49bitcat/nileswan/legacy/pcb/snapeda/models/SIT8021AI-J4-XXS-24.000000E.step

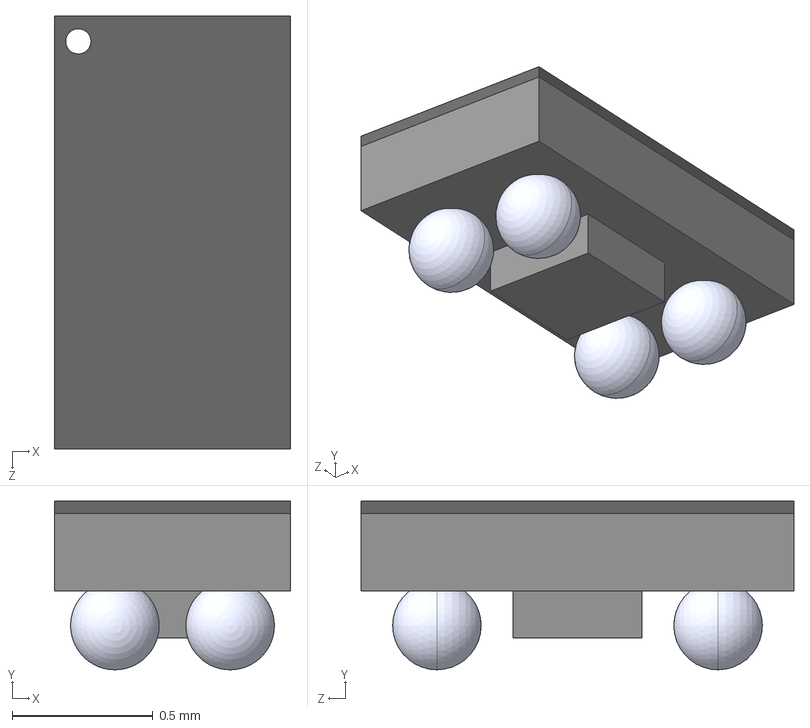
[picture p17: CAD file, 2025-10-31, an earlier design]
legacy/pcb/snapeda/models/SIT8021AI-J4-XXS-24.000000E.step
0.84 x 0.6 x 1.54 mm
