49bitcat/nileswan/legacy/pcb/snapeda/models/W25Q16JVZPIQ.STEP

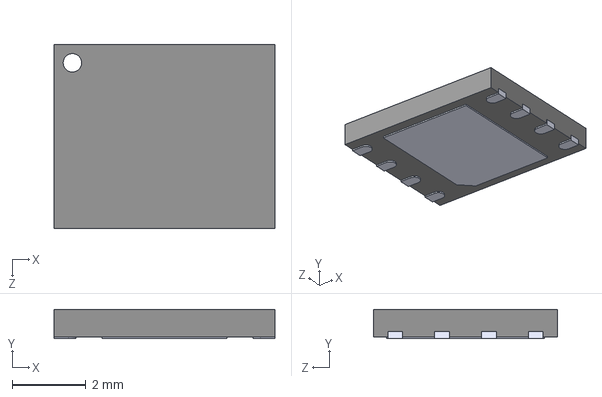
[picture p18: CAD file, 2025-10-31, an earlier design]
legacy/pcb/snapeda/models/W25Q16JVZPIQ.STEP
6.00 x 0.8 x 5.00 mm
