49bitcat/nileswan/legacy/pcb/snapeda/models/TPS3619-50DGK.step

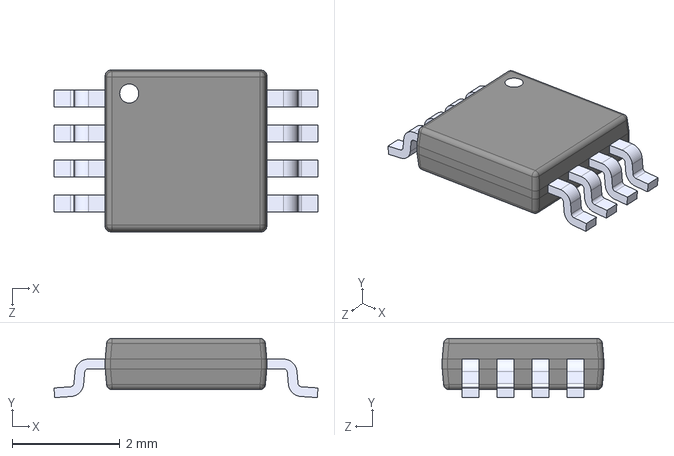
[picture p19: CAD file, 2025-10-31, an earlier design]
legacy/pcb/snapeda/models/TPS3619-50DGK.step
4.90 x 1.10 x 3.00 mm
