49bitcat/nileswan/firmware/src/mcu.c

/**
 * Copyright (c) 2024 Adrian "asie" Siekierka
 *
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
 * You should have received a copy of the GNU General Public License along
 * with Nileswan MCU. If not, see <https://www.gnu.org/licenses/>.
 */

#include <stdbool.h>
#include <stddef.h>
#include <stdint.h>
#include <stm32u073xx.h>
#include <stm32u0xx_ll_adc.h>
#include <stm32u0xx_ll_gpio.h>
#include <stm32u0xx_ll_pwr.h>
#include <stm32u0xx_ll_rcc.h>
#include <stm32u0xx_ll_system.h>

#include "mcu.h"
#include "config.h"
#include "nvram.h"
#include "rtc.h"
#include "spi.h"
#include "tusb.h"
#include "accel.h"

typedef enum {
    USB_INIT_STATUS_OFF = 0,
    USB_INIT_STATUS_REQUEST_ON = 1,
    USB_INIT_STATUS_ON = 2,
    USB_INIT_STATUS_REQUEST_OFF = 3
} usb_init_status_t;

static bool usb_enabled = false;
static volatile uint8_t usb_init_status = USB_INIT_STATUS_OFF;

static void __mcu_usb_on_power_change(void) {
    if (mcu_usb_is_power_connected() && usb_enabled) {
        if (usb_init_status == USB_INIT_STATUS_OFF) {
            usb_init_status = USB_INIT_STATUS_REQUEST_ON;
        } else if (usb_init_status == USB_INIT_STATUS_ON) {
            USB->BCDR |= USB_BCDR_DPPU;
        }
    } else {
        if (usb_init_status == USB_INIT_STATUS_ON) {
            usb_init_status = USB_INIT_STATUS_REQUEST_OFF;
        }
    }
}

#define BATTERY_QUERY_DELAY (48 / 3)

enum {
    BATTERY_PRESENT_CACHE_UNKNOWN = 0,
    BATTERY_PRESENT_CACHE_NO,
    BATTERY_PRESENT_CACHE_YES
};

static uint8_t battery_present_cache = BATTERY_PRESENT_CACHE_UNKNOWN;

uint16_t mcu_power_query_battery_voltage(void) {
    int i;

    // Before running an ADC measurement, we need to rule out the case of the
    // battery being removed (floating BAT pin). However, as using a pull-down
    // here is electrically costly, we want to avoid doing it more often than
    // necessary. With this in mind, the following assumptions are made:
    //
    // - If the MCU is running in a console, the cartridge is designed so that
    //   the battery should not be removed. As such, we can make an assumption
    //   that it is either present or not present after the first check.
    // - If the MCU is running outside of a console, we can assume that the
    //   battery is inserted; otherwise, the code would not be running.
    if (!mcu_power_is_running_on_battery()) {
        if (battery_present_cache == BATTERY_PRESENT_CACHE_UNKNOWN) {
            // Figure out if the battery is present.
            LL_GPIO_SetPinMode(GPIOB, MCU_PIN_BAT, LL_GPIO_MODE_INPUT);
            LL_GPIO_SetPinPull(GPIOB, MCU_PIN_BAT, LL_GPIO_PULL_DOWN);
            i = BATTERY_QUERY_DELAY; while (i--) asm("");
            bool battery_present = LL_GPIO_IsInputPinSet(GPIOB, MCU_PIN_BAT);
            LL_GPIO_SetPinMode(GPIOB, MCU_PIN_BAT, LL_GPIO_MODE_ANALOG);
            LL_GPIO_SetPinPull(GPIOB, MCU_PIN_BAT, LL_GPIO_PULL_NO);
            battery_present_cache = battery_present ? BATTERY_PRESENT_CACHE_YES : BATTERY_PRESENT_CACHE_NO;
        }

        if (battery_present_cache == BATTERY_PRESENT_CACHE_NO) {
            return 0;
        }
    } else {
        battery_present_cache = BATTERY_PRESENT_CACHE_YES;
    }

    i = BATTERY_QUERY_DELAY; while (i--) asm("");

    // Once we have figured out that the battery is present,
    // measure the exact voltage if enabled.
#ifdef CONFIG_ENABLE_ADC
    if (LL_ADC_IsEnabled(ADC1)) {
        LL_ADC_REG_StartConversion(ADC1);
        while (!LL_ADC_IsActiveFlag_EOC(ADC1));
        return LL_ADC_REG_ReadConversionData12(ADC1);
    }
#endif
    return 3725; // ~3.0V
}

static void __mcu_bat_on_power_change(void) {
    // If battery inserted and running on battery, go to Standby
    if (mcu_power_is_running_on_battery() && mcu_power_is_battery_inserted()) {
        mcu_shutdown();
    }
}

void PVD_PVM_IRQHandler(void) {
    mcu_shutdown();
}

void EXTI2_3_IRQHandler(void) {
    if ((EXTI->RPR1 & EXTI_RPR1_RPIF2) != 0) {
        EXTI->RPR1 = EXTI_RPR1_RPIF2;
        mcu_spi_irq_set(MCU_SPI_IRQ_TF_REMOVE);
    }

    if ((EXTI->FPR1 & EXTI_FPR1_FPIF2) != 0) {
        EXTI->FPR1 = EXTI_FPR1_FPIF2;
        mcu_spi_irq_set(MCU_SPI_IRQ_TF_INSERT);
    }
}

void EXTI4_15_IRQHandler(void) {
    if ((EXTI->RPR1 & EXTI_RPR1_RPIF5) != 0) {
        EXTI->RPR1 = EXTI_RPR1_RPIF5;
        __mcu_usb_on_power_change();
    }

    if ((EXTI->FPR1 & EXTI_FPR1_FPIF5) != 0) {
        EXTI->FPR1 = EXTI_FPR1_FPIF5;
        __mcu_usb_on_power_change();
    }

    if ((EXTI->RPR1 & EXTI_RPR1_RPIF7) != 0) {
        EXTI->RPR1 = EXTI_RPR1_RPIF7;
        __mcu_bat_on_power_change();
    }

    if ((EXTI->FPR1 & EXTI_FPR1_FPIF7) != 0) {
        EXTI->FPR1 = EXTI_FPR1_FPIF7;
        __mcu_bat_on_power_change();
    }
}

static uint16_t last_clock_speed = 0xFFFF;
static uint8_t busy_pin_delay = 0;

#define FINISH_BUSY_MIN_CLOCKS 10
#define FINISH_BUSY_CLOCKS_PER_ITERATION 3

__attribute__((noinline))
void mcu_fpga_finish_busy(void) {
    // ~10 cycles + 3 cycles per iteration
    int i = busy_pin_delay;
    while (i--) asm("");
    LL_GPIO_SetPinMode(GPIOA, MCU_PIN_FPGA_BUSY, LL_GPIO_MODE_ANALOG);
}

void mcu_update_clock_speed(void) {
    uint32_t msi_range;
    uint32_t ahb_freq;
    uint32_t ahb_divisor;
    uint32_t apb_divisor;

    // Calculate target MCU speed
#ifdef CONFIG_MCU_FORCE_MAX_CLOCK
    msi_range = LL_RCC_MSIRANGE_11;
    ahb_freq = 48 * 1000 * 1000;
    ahb_divisor = LL_RCC_SYSCLK_DIV_1;
    apb_divisor = LL_RCC_APB1_DIV_1;
#else
    msi_range = LL_RCC_MSIRANGE_8;
    ahb_freq = 16 * 1000 * 1000;
    ahb_divisor = LL_RCC_SYSCLK_DIV_1;
    apb_divisor = LL_RCC_APB1_DIV_1;

    bool usb_power_connected = mcu_usb_is_power_connected() && usb_enabled;
    if (usb_power_connected
#ifndef CONFIG_ENABLE_CLOCK_MSI_USB
        && tud_mounted()
#endif
    ) {
        // If USB is plugged in, accelerate the CPU.
        switch (mcu_spi_get_freq()) {
            default:
                // 48 MHz AHB, 48 MHz APB
                msi_range = LL_RCC_MSIRANGE_11;
                ahb_freq = 48 * 1000 * 1000;
                break;
            case MCU_SPI_FREQ_384KHZ:
                // SPI bus constrained to 384 KHz - fast USB communication doesn't matter much.
                // 24 MHz AHB, 24 MHz APB
#ifdef CONFIG_ENABLE_CLOCK_MSI_USB
                msi_range = LL_RCC_MSIRANGE_11;
                ahb_divisor = LL_RCC_SYSCLK_DIV_2;
#else
                msi_range = LL_RCC_MSIRANGE_9;
#endif
                ahb_freq = 24 * 1000 * 1000;
                break;
        }
    } else {
        switch (mcu_spi_get_freq()) {
            case MCU_SPI_FREQ_384KHZ:
                if (usb_power_connected)
                    break;

                // For slow SPI transfers, we can clock the APB bus down.
                // 16 MHz AHB, 4 MHz APB
                apb_divisor = LL_RCC_APB1_DIV_4;

                if (mcu_spi_get_mode() == MCU_SPI_MODE_EEPROM || mcu_spi_get_mode() == MCU_SPI_MODE_CDC_OUTPUT) {
                    // 384 KHz SPI output only mode (EEPROM, USB CDC output w/o USB connected)
                    // 1 MHz AHB, 1 MHz APB
                    msi_range = LL_RCC_MSIRANGE_4;
                    ahb_freq = 1 * 1000 * 1000;
                    apb_divisor = LL_RCC_APB1_DIV_1;
                } else if (mcu_spi_get_mode() == MCU_SPI_MODE_RTC) {
                    // FIXME: The FPGA RTC logic appears to break down when the APB frequency is not divisible by 384 KHz.
                    // FIXME: At frequencies below 24 MHz, the RTC stability test still fails after a few hundred thousand attempts.
                    msi_range = LL_RCC_MSIRANGE_9;
                    ahb_freq = 24 * 1000 * 1000;
                    ahb_divisor = LL_RCC_SYSCLK_DIV_1;
                    apb_divisor = LL_RCC_APB1_DIV_1;
                } else {
                    // Other modes (f.e. native MCU mode)
                    // 8 MHz AHB, 4 MHz APB
                    msi_range = LL_RCC_MSIRANGE_7;
                    ahb_freq = 8 * 1000 * 1000;
                    apb_divisor = LL_RCC_APB1_DIV_2;
                }
                break;
            case MCU_SPI_FREQ_6MHZ:
                // 6 MHz SPI transfers.
                // 24 MHz AHB, 12/24 MHz APB
                msi_range = LL_RCC_MSIRANGE_9;
                ahb_freq = 24 * 1000 * 1000;
                if (!usb_power_connected)
                    apb_divisor = LL_RCC_APB1_DIV_2;
                break;
            case MCU_SPI_FREQ_24MHZ:
                // 24 MHz SPI transfers.
                // 48 MHz AHB, 48 MHz APB
                msi_range = LL_RCC_MSIRANGE_11;
                ahb_freq = 48 * 1000 * 1000;
                break;
        }
    }
#endif

    uint32_t apb_freq = ahb_freq;
    switch (apb_divisor) {
    case LL_RCC_APB1_DIV_1: break;
    case LL_RCC_APB1_DIV_2: apb_freq /= 2; break;
    case LL_RCC_APB1_DIV_4: apb_freq /= 4; break;
    case LL_RCC_APB1_DIV_8: apb_freq /= 8; break;
    case LL_RCC_APB1_DIV_16: apb_freq /= 16; break;
    }
    accel_adjust_i2c_timing(apb_freq);

    if ((msi_range | ahb_divisor) == last_clock_speed) {
        LL_RCC_SetAPB1Prescaler(apb_divisor);
        return;
    }

    bool use_high_flash_latency = msi_range > LL_RCC_MSIRANGE_9 && ahb_divisor == LL_RCC_SYSCLK_DIV_1;
    bool use_high_voltage_scale = msi_range >= LL_RCC_MSIRANGE_8;
    bool use_high_power_run = msi_range >= LL_RCC_MSIRANGE_5;

    LL_RCC_SetAPB1Prescaler(LL_RCC_APB1_DIV_1);

    if (use_high_power_run) {
        LL_PWR_DisableLowPowerRunMode();
        while (LL_PWR_IsEnabledLowPowerRunMode());
    }

    if (use_high_voltage_scale) {
        LL_PWR_SetRegulVoltageScaling(LL_PWR_REGU_VOLTAGE_SCALE1);
        while (LL_PWR_IsActiveFlag_VOS());
    }

    if (use_high_flash_latency) {
        LL_FLASH_SetLatency(LL_FLASH_LATENCY_1);
        while (LL_FLASH_GetLatency() != LL_FLASH_LATENCY_1);
    }

    LL_RCC_SetAHBPrescaler(LL_RCC_SYSCLK_DIV_1);

    while (!LL_RCC_MSI_IsReady());
    LL_RCC_MSI_SetRange(msi_range);

    if (!use_high_flash_latency)
        LL_FLASH_SetLatency(LL_FLASH_LATENCY_0);

    if (!use_high_voltage_scale) {
        LL_PWR_SetRegulVoltageScaling(LL_PWR_REGU_VOLTAGE_SCALE2);
        while (LL_PWR_IsActiveFlag_VOS());
    }

    if (!use_high_power_run) {
        LL_PWR_EnableLowPowerRunMode();
        while (!LL_PWR_IsEnabledLowPowerRunMode());
    }

    LL_RCC_SetAHBPrescaler(ahb_divisor);
    LL_RCC_SetAPB1Prescaler(apb_divisor);
    LL_SetSystemCoreClock(ahb_freq);
    LL_Init1msTick(ahb_freq);

#ifdef CONFIG_ENABLE_ADC
    uint32_t adc_clock = LL_ADC_CLOCK_SYNC_PCLK_DIV1;
    if (msi_range >= LL_RCC_MSIRANGE_10) {
        adc_clock = LL_ADC_CLOCK_SYNC_PCLK_DIV4;
    } else if (msi_range >= LL_RCC_MSIRANGE_8) {
        adc_clock = LL_ADC_CLOCK_SYNC_PCLK_DIV2;
    }
    LL_ADC_SetClock(ADC1, adc_clock);
#endif

    int clocks = (ahb_freq / (384*1000)) - FINISH_BUSY_MIN_CLOCKS;
    busy_pin_delay = clocks > 0 ? ((uint32_t)(clocks + FINISH_BUSY_CLOCKS_PER_ITERATION - 1) / FINISH_BUSY_CLOCKS_PER_ITERATION) : 0;

    last_clock_speed = (msi_range | ahb_divisor);
}

void mcu_init(void) {
    // Initialize clocks
    LL_RCC_MSI_Enable();

    LL_APB1_GRP1_EnableClock(LL_APB1_GRP1_PERIPH_PWR);
    LL_LPM_EnableSleep();

    while (!LL_RCC_MSI_IsReady());
    LL_RCC_MSI_EnableRangeSelection();

    mcu_update_clock_speed();

    LL_RCC_SetSysClkSource(LL_RCC_SYS_CLKSOURCE_MSI);
    while(LL_RCC_GetSysClkSource() != LL_RCC_SYS_CLKSOURCE_STATUS_MSI);

    LL_RCC_SetAHBPrescaler(LL_RCC_SYSCLK_DIV_1);

#ifdef TARGET_U0
    LL_APB1_GRP2_EnableClock(LL_APB1_GRP2_PERIPH_SYSCFG);
#else
    LL_RCC_SetAPB2Prescaler(LL_RCC_APB2_DIV_1);
    LL_APB2_GRP1_EnableClock(LL_APB2_GRP1_PERIPH_SYSCFG);
#endif

    LL_SYSTICK_SetClkSource(LL_SYSTICK_CLKSOURCE_HCLK);
    LL_SYSTICK_EnableIT();

    LL_PWR_EnableBkUpAccess();

    LL_IOP_GRP1_EnableClock(LL_IOP_GRP1_PERIPH_GPIOA | LL_IOP_GRP1_PERIPH_GPIOB);

    // Initialize input pins
    LL_GPIO_SetPinPull(GPIOA, MCU_PIN_TF_DETECT, LL_GPIO_PULL_UP);
    LL_GPIO_SetPinSpeed(GPIOA, MCU_PIN_TF_DETECT, LL_GPIO_SPEED_FREQ_LOW);
    LL_GPIO_SetPinMode(GPIOA, MCU_PIN_TF_DETECT, LL_GPIO_MODE_INPUT);

    // Initialize input pins: VBUS sensing
    LL_GPIO_SetPinPull(GPIOB, MCU_PIN_USB_POWER, LL_GPIO_PULL_DOWN);
    LL_GPIO_SetPinSpeed(GPIOB, MCU_PIN_USB_POWER, LL_GPIO_SPEED_FREQ_LOW);
    LL_GPIO_SetPinMode(GPIOB, MCU_PIN_USB_POWER, LL_GPIO_MODE_INPUT);

    // Initialize input pins: battery sensing
    LL_GPIO_SetPinPull(GPIOB, MCU_PIN_BAT, LL_GPIO_PULL_NO);
    LL_GPIO_SetPinSpeed(GPIOB, MCU_PIN_BAT, LL_GPIO_SPEED_FREQ_LOW);
    LL_GPIO_SetPinMode(GPIOB, MCU_PIN_BAT, LL_GPIO_MODE_ANALOG);
    LL_GPIO_SetPinPull(GPIOB, MCU_PIN_RUNS_ON_BAT, LL_GPIO_PULL_UP);
    LL_GPIO_SetPinSpeed(GPIOB, MCU_PIN_RUNS_ON_BAT, LL_GPIO_SPEED_FREQ_LOW);
    LL_GPIO_SetPinMode(GPIOB, MCU_PIN_RUNS_ON_BAT, LL_GPIO_MODE_INPUT);

    // Keep the pulls active in Standby mode
    PWR->PUCRA = 0;
    PWR->PUCRB = MCU_PIN_RUNS_ON_BAT;
    PWR->PDCRA = 0;
    PWR->PDCRB = MCU_PIN_USB_POWER;
    LL_PWR_EnablePUPDCfg();
    LL_PWR_EnableSRAMRetention();

    // Enable PVD - if we're below 2.9 V, we are definitely not plugged
    // into a console, so we can short circuit to powering down.
    LL_PWR_SetPVDLevel(LL_PWR_PVDLEVEL_6);
    LL_PWR_EnablePVD();

    LL_EXTI_EnableRisingTrig_0_31(LL_EXTI_LINE_16);
    LL_EXTI_EnableIT_0_31(LL_EXTI_LINE_16);
    NVIC_SetPriority(PVD_PVM_IRQn, MCU_IRQ_PRIORITY_PVD);
    NVIC_EnableIRQ(PVD_PVM_IRQn);

#ifdef CONFIG_ENABLE_ADC
    // Initialize ADC
    LL_APB1_GRP2_EnableClock(LL_APB1_GRP2_PERIPH_ADC);
    LL_ADC_SetResolution(ADC1, LL_ADC_RESOLUTION_12B);
    LL_ADC_SetDataAlignment(ADC1, LL_ADC_DATA_ALIGN_RIGHT);
    LL_ADC_REG_SetContinuousMode(ADC1, LL_ADC_REG_CONV_SINGLE);
    if (LL_ADC_REG_GetSequencerConfigurable(ADC1) != LL_ADC_REG_SEQ_FIXED) {
        LL_ADC_REG_SetSequencerConfigurable(ADC1, LL_ADC_REG_SEQ_FIXED);
        while (!LL_ADC_IsActiveFlag_CCRDY(ADC1));
        LL_ADC_ClearFlag_CCRDY(ADC1);
    }
    LL_ADC_SetSamplingTimeCommonChannels(ADC1, LL_ADC_SAMPLINGTIME_COMMON_1, LL_ADC_SAMPLINGTIME_39CYCLES_5);
    LL_ADC_SetChannelSamplingTime(ADC1, MCU_PIN_BAT_CHANNEL_ADC, LL_ADC_SAMPLINGTIME_COMMON_1);
    /* LL_ADC_SetOverSamplingDiscont(ADC1, LL_ADC_OVS_REG_CONT);
    LL_ADC_SetOverSamplingScope(ADC1, LL_ADC_OVS_GRP_REGULAR_CONTINUED);
    LL_ADC_ConfigOverSamplingRatioShift(ADC1, LL_ADC_OVS_RATIO_8, LL_ADC_OVS_SHIFT_RIGHT_3); */
    LL_ADC_REG_SetSequencerChannels(ADC1, MCU_PIN_BAT_CHANNEL_ADC);
    while (!LL_ADC_IsActiveFlag_CCRDY(ADC1));
    LL_ADC_ClearFlag_CCRDY(ADC1);
    LL_ADC_SetTriggerFrequencyMode(ADC1, LL_ADC_TRIGGER_FREQ_LOW);
    // Start ADC regulator
    LL_ADC_EnableInternalRegulator(ADC1);

    // Wait for ADC regulator to stabilize
    int i = LL_ADC_DELAY_INTERNAL_REGUL_STAB_US / 3;
    while (i--) asm("");

    // Start ADC calibration
    LL_ADC_REG_SetDMATransfer(ADC1, LL_ADC_REG_DMA_TRANSFER_NONE);
    LL_ADC_StartCalibration(ADC1);

    while (LL_ADC_IsCalibrationOnGoing(ADC1));
    i = LL_ADC_DELAY_CALIB_ENABLE_ADC_CYCLES * 4;
    while (i--) asm("");

    // Configuring ADC low power mode must be done after calibration, but before
    // enabling the ADC itself. In addition, if AUTOFF = 1, the ADRDY flag is not
    // set after enabling the ADC.
    LL_ADC_SetLowPowerMode(ADC1, LL_ADC_LP_AUTOPOWEROFF);
    LL_ADC_Enable(ADC1);
    while (!LL_ADC_IsEnabled(ADC1));
#else
    LL_mDelay(1);
#endif
    __mcu_bat_on_power_change();

    // Initialize SPI pins
    for (uint32_t pin = LL_GPIO_PIN_4; pin <= LL_GPIO_PIN_7; pin <<= 1) {
#ifdef TARGET_U0
        LL_GPIO_SetAFPin_0_7(MCU_PORT_SPI, pin, LL_GPIO_AF_5); // SPI1
#else
        LL_GPIO_SetAFPin_0_7(MCU_PORT_SPI, pin, LL_GPIO_AF_0);
#endif
        LL_GPIO_SetPinOutputType(MCU_PORT_SPI, pin, LL_GPIO_OUTPUT_PUSHPULL);
        LL_GPIO_SetPinSpeed(MCU_PORT_SPI, pin, LL_GPIO_SPEED_FREQ_LOW);
        LL_GPIO_SetPinPull(MCU_PORT_SPI, pin, LL_GPIO_PULL_NO);
        LL_GPIO_SetPinMode(MCU_PORT_SPI, pin, LL_GPIO_MODE_ALTERNATE);
    }

    // Initialize I2C pins
    for (uint32_t pin = LL_GPIO_PIN_9; pin <= LL_GPIO_PIN_10; pin <<= 1) {
        LL_GPIO_SetAFPin_8_15(MCU_PORT_I2C, pin, LL_GPIO_AF_4); // I2C1

        LL_GPIO_SetPinOutputType(MCU_PORT_I2C, pin, LL_GPIO_OUTPUT_OPENDRAIN);
        // needs to work against relatively low impedance pull-down
        LL_GPIO_SetPinSpeed(MCU_PORT_I2C, pin, LL_GPIO_SPEED_FREQ_VERY_HIGH);
        LL_GPIO_SetPinPull(MCU_PORT_I2C, pin, LL_GPIO_PULL_UP);
        LL_GPIO_SetPinMode(MCU_PORT_I2C, pin, LL_GPIO_MODE_ALTERNATE);
    }

    // Initialize output pins
    LL_GPIO_SetPinMode(GPIOA, MCU_PIN_FPGA_IRQ, LL_GPIO_MODE_OUTPUT);
    LL_GPIO_SetPinOutputType(GPIOA, MCU_PIN_FPGA_IRQ, LL_GPIO_OUTPUT_PUSHPULL);
    LL_GPIO_SetPinPull(GPIOA, MCU_PIN_FPGA_IRQ, LL_GPIO_PULL_NO);
    LL_GPIO_SetPinSpeed(GPIOA, MCU_PIN_FPGA_IRQ, LL_GPIO_SPEED_FREQ_LOW);
    mcu_fpga_irq_clear();

    // BUSY is only pulled high, never low
    LL_GPIO_SetPinMode(GPIOA, MCU_PIN_FPGA_BUSY, LL_GPIO_MODE_ANALOG);
    LL_GPIO_SetPinOutputType(GPIOA, MCU_PIN_FPGA_BUSY, LL_GPIO_OUTPUT_PUSHPULL);
    LL_GPIO_SetPinPull(GPIOA, MCU_PIN_FPGA_BUSY, LL_GPIO_PULL_NO);
    LL_GPIO_SetPinSpeed(GPIOA, MCU_PIN_FPGA_BUSY, LL_GPIO_SPEED_FREQ_LOW);
    LL_GPIO_SetOutputPin(GPIOA, MCU_PIN_FPGA_BUSY);

    // Initialize GPIO interrupts
    LL_EXTI_SetEXTISource(LL_EXTI_CONFIG_PORTA, LL_EXTI_CONFIG_LINE2);
    LL_EXTI_SetEXTISource(LL_EXTI_CONFIG_PORTB, LL_EXTI_CONFIG_LINE5);
    LL_EXTI_SetEXTISource(LL_EXTI_CONFIG_PORTB, LL_EXTI_CONFIG_LINE7);
    LL_EXTI_EnableRisingTrig_0_31(LL_EXTI_LINE_2 | LL_EXTI_LINE_5 | LL_EXTI_LINE_7);
    LL_EXTI_EnableFallingTrig_0_31(LL_EXTI_LINE_2 | LL_EXTI_LINE_5 | LL_EXTI_LINE_7);
    LL_EXTI_EnableIT_0_31(LL_EXTI_LINE_2 | LL_EXTI_LINE_5 | LL_EXTI_LINE_7);

    NVIC_SetPriority(EXTI2_3_IRQn, MCU_IRQ_PRIORITY_DEFAULT);
    NVIC_EnableIRQ(EXTI2_3_IRQn);

    NVIC_SetPriority(EXTI4_15_IRQn,  MCU_IRQ_PRIORITY_DEFAULT);
    NVIC_EnableIRQ(EXTI4_15_IRQn);

    // Initialize USB
    NVIC_SetPriority(USB_DRD_FS_IRQn, MCU_IRQ_PRIORITY_USB);
    mcu_usb_set_enabled(true);

    // Initialize SPI
#ifdef TARGET_U0
    LL_APB1_GRP2_EnableClock(LL_APB1_GRP2_PERIPH_SPI1);

    RCC->APBSMENR2 &= ~(RCC_APBSMENR2_ADCSMEN | RCC_APBSMENR2_SYSCFGSMEN);
#else
    LL_APB2_GRP1_EnableClock(LL_APB2_GRP1_PERIPH_SPI1);
#endif

    while (!LL_PWR_IsEnabledBkUpAccess());
}

void mcu_exit_native_mode(void) {
    accel_deinit();

#ifdef CONFIG_ENABLE_ADC
    // Power down ADC
    LL_ADC_Disable(ADC1);
    LL_ADC_DisableInternalRegulator(ADC1);
    LL_APB1_GRP2_DisableClock(LL_APB1_GRP2_PERIPH_ADC);
#endif

    // Power down no longer used inputs
    LL_GPIO_SetPinMode(GPIOA, MCU_PIN_TF_DETECT, LL_GPIO_MODE_ANALOG);
}

void mcu_usb_set_enabled(bool enabled) {
    usb_enabled = enabled;
    __mcu_usb_on_power_change();
}

bool mcu_usb_is_powered(void) {
    return usb_init_status == USB_INIT_STATUS_ON;
}

bool mcu_usb_is_active(void) {
    return usb_init_status == USB_INIT_STATUS_ON && tud_connected() && !tud_suspended();
}

void SysTick_Handler(void) {
}

void USB_DRD_FS_IRQHandler(void) {
    if (usb_init_status == USB_INIT_STATUS_ON) {
        tud_int_handler(0);
    } else {
        // Clear pending interrupts while in the process of disabling the USB hardware
        USB->ISTR = 0;
    }
}

static void __mcu_usb_power_on(void) {
#ifdef CONFIG_ENABLE_CLOCK_MSI_USB
    rtc_enable_lse_clock();
    if (LL_RCC_LSE_IsReady()) {
        LL_RCC_MSI_EnablePLLMode();
        LL_RCC_SetUSBClockSource(LL_RCC_USB_CLKSOURCE_MSI);
    } else
#endif
    {
        // Enable 48 MHz internal oscillator
        LL_RCC_HSI48_Enable();
        while (!LL_RCC_HSI48_IsReady());
        LL_RCC_SetUSBClockSource(LL_RCC_USB_CLKSOURCE_HSI48);

        // Enable clock recovery system
        LL_APB1_GRP1_EnableClock(LL_APB1_GRP1_PERIPH_CRS);
        LL_CRS_ConfigSynchronization(LL_CRS_HSI48CALIBRATION_DEFAULT,
                                        LL_CRS_ERRORLIMIT_DEFAULT,
                                        LL_CRS_RELOADVALUE_DEFAULT,
                                        LL_CRS_SYNC_DIV_1 | LL_CRS_SYNC_SOURCE_USB | LL_CRS_SYNC_POLARITY_RISING);

        LL_CRS_EnableFreqErrorCounter();
        LL_CRS_EnableAutoTrimming();
    }

    LL_PWR_EnableVddUSB();

    // Enable USB clock
    LL_APB1_GRP1_EnableClock(LL_APB1_GRP1_PERIPH_USB);
}

static void __mcu_usb_power_off(void) {
    LL_APB1_GRP1_DisableClock(LL_APB1_GRP1_PERIPH_USB);

    LL_PWR_DisableVddUSB();

    LL_CRS_DisableAutoTrimming();
    LL_CRS_DisableFreqErrorCounter();
    LL_APB1_GRP1_DisableClock(LL_APB1_GRP1_PERIPH_CRS);

    LL_RCC_SetUSBClockSource(LL_RCC_USB_CLKSOURCE_PLL);
    LL_RCC_HSI48_Disable();
}

void mcu_usb_power_task(void) {
    if (usb_init_status == USB_INIT_STATUS_REQUEST_ON) {
        tusb_rhport_init_t dev_init = {
            .role = TUSB_ROLE_DEVICE,
            .speed = TUSB_SPEED_AUTO
        };

        __mcu_usb_power_on();
        // set before tusb_init so USB peripheral interrupts are serviced correctly
        usb_init_status = USB_INIT_STATUS_ON;
        tusb_init(0, &dev_init);

        mcu_update_clock_speed();
        __mcu_usb_on_power_change();
    } else if (usb_init_status == USB_INIT_STATUS_REQUEST_OFF) {
        USB->BCDR &= ~USB_BCDR_DPPU;

        tusb_deinit(0);
        __mcu_usb_power_off();
        usb_init_status = USB_INIT_STATUS_OFF;

        mcu_update_clock_speed();
    }
}

void mcu_shutdown(void) {
    LL_LPM_EnableDeepSleep();

    LL_PWR_DisableBkUpAccess();
    if (nvram_retention_required() || LL_RCC_GetRTCClockSource() == LL_RCC_RTC_CLKSOURCE_LSI) {
        LL_PWR_EnableSRAMRetention();
        LL_PWR_SetPowerMode(LL_PWR_MODE_STANDBY);
        while (!LL_PWR_IsEnabledSRAMRetention());
    } else {
        LL_PWR_DisableSRAMRetention();
        LL_PWR_SetPowerMode(LL_PWR_MODE_SHUTDOWN);
        while (LL_PWR_IsEnabledSRAMRetention());
    }

    while (LL_PWR_IsEnabledBkUpAccess());

    if (usb_init_status != USB_INIT_STATUS_OFF) {
        usb_init_status = USB_INIT_STATUS_REQUEST_OFF;
        mcu_usb_power_task();
    }

    __disable_irq();

    while(1) __WFI();
}

void mcu_reset_backup_domain(void) {
    uint32_t save_id = TAMP->BKP8R;

    LL_RCC_ForceBackupDomainReset();
    LL_RCC_ReleaseBackupDomainReset();

    TAMP->BKP8R = save_id;
}

void mcu_update_dma_clock(void) {
    if (mcu_spi_get_mode() != MCU_SPI_MODE_EEPROM || accel_is_enabled()) {
        LL_AHB1_GRP1_EnableClock(LL_AHB1_GRP1_PERIPH_DMA1);
    } else {
        LL_AHB1_GRP1_DisableClock(LL_AHB1_GRP1_PERIPH_DMA1);
    }
}

void tud_mount_cb(void) {
    mcu_update_clock_speed();
}

void tud_umount_cb(void) {
    mcu_update_clock_speed();
}

/* void tud_suspend_cb(bool remote_wakeup_en) {
    mcu_update_clock_speed();
}

void tud_resume_cb(void) {
    mcu_update_clock_speed();
} */

void tusb_time_delay_ms_api(uint32_t ms) {
    LL_mDelay(ms);
}
