49bitcat/nileswan/firmware/src/accel.c

/**
 * Copyright (c) 2024 Kemal Afzal
 *
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
 * You should have received a copy of the GNU General Public License along
 * with Nileswan MCU. If not, see <https://www.gnu.org/licenses/>.
 */
#include "accel.h"

#include "config.h"
#include "cdc.h"
#include "spi.h"

#include <stdint.h>
#include <stm32u073xx.h>
#include <stm32u0xx_ll_dma.h>
#include <stm32u0xx_ll_utils.h>
#include <string.h>

#include <stm32u0xx_ll_i2c.h>
#include <stm32u0xx_ll_tim.h>

#define MXC400_I2C_ADDR 0x15<<1

#define MXC400_REG_CONTROL 0x0D
#define MXC400_POWERDOWN (1<<0)

#define MXC400_REG_OUT_START 0x03

// timer ticks in microseconds
#define TIMERHZ (1000*1000)

static uint32_t timing = 0;

static bool polling = false;

typedef enum {
    state_Idle,
    state_SendAddr,
    state_ReadAccelState
} State;
static volatile State state = state_Idle;

static uint32_t timer_prescaler;

static volatile uint8_t visible_accel_state = 0;
static int16_t accel_data[2][3] = {{0, 0, -(1<<10)}, {0, 0, -(1<<10)}};

static bool chip_detected = false;

void DMA1_Ch4_7_DMA2_Ch1_5_DMAMUX_OVR_IRQHandler(void) {
    _Static_assert(MCU_DMA_CHANNEL_I2C == LL_DMA_CHANNEL_4, "Assumed I2C uses DMA channel 4");

    uint32_t write_state = visible_accel_state ^ 1;
    for (int i = 0; i < 3; i++)
        accel_data[write_state][i] =
            (int16_t)__builtin_bswap16(accel_data[write_state][i]) >> 4;
#ifdef CONFIG_DEBUG_ACCEL
    //cdc_debug("done %d %d %d\n", accel_data[write_state][0], accel_data[write_state][1], accel_data[write_state][2]);
#endif

    LL_DMA_ClearFlag_TC4(DMA1);
    LL_DMA_DisableChannel(DMA1, MCU_DMA_CHANNEL_I2C);
    state = state_Idle;

    visible_accel_state = write_state;
}

static void __i2c_disable(void) {
    LL_I2C_Disable(MCU_PERIPH_I2C);
    while (LL_I2C_IsEnabled(MCU_PERIPH_I2C));
}

static bool __i2c_err_detected(void) {
    return MCU_PERIPH_I2C->ISR & (I2C_ISR_BERR | I2C_ISR_ARLO | I2C_ISR_OVR | I2C_ISR_NACKF);
}

static void __i2c_err_clear(void) {
    MCU_PERIPH_I2C->ICR = I2C_ICR_BERRCF | I2C_ICR_ARLOCF | I2C_ICR_OVRCF | I2C_ICR_NACKCF;
}

void I2C1_IRQHandler(void) {
#ifdef CONFIG_DEBUG_ACCEL
    //cdc_debug("interrupt %x\n", MCU_PERIPH_I2C->ISR);
#endif
    State cur_state = state;
    if (__i2c_err_detected()) {
#ifdef CONFIG_DEBUG_ACCEL
        cdc_debug("I2C error %x\n", MCU_PERIPH_I2C->ISR);
#endif
        __i2c_err_clear();
        state = state_Idle;
    } else if (cur_state == state_SendAddr) {
        if (LL_I2C_IsActiveFlag_TC(MCU_PERIPH_I2C)) {
#ifdef CONFIG_DEBUG_ACCEL
            //cdc_debug("tc, start read\n");
#endif

            LL_DMA_ConfigAddresses(DMA1,
                MCU_DMA_CHANNEL_I2C,
                (uint32_t) &accel_data[visible_accel_state^1],
                LL_I2C_DMA_GetRegAddr(MCU_PERIPH_I2C, LL_I2C_DMA_REG_DATA_RECEIVE),
                LL_DMA_DIRECTION_MEMORY_TO_PERIPH);
            LL_DMA_SetDataLength(DMA1, MCU_DMA_CHANNEL_I2C, sizeof(accel_data[0]));

            LL_DMA_EnableChannel(DMA1, MCU_DMA_CHANNEL_I2C);
            LL_I2C_HandleTransfer(MCU_PERIPH_I2C,
                MXC400_I2C_ADDR,
                LL_I2C_ADDRSLAVE_7BIT,
                6,
                LL_I2C_MODE_AUTOEND,
                LL_I2C_GENERATE_RESTART_7BIT_READ);

            state = state_ReadAccelState;
        } else if (LL_I2C_IsActiveFlag_TXE(MCU_PERIPH_I2C)) {
            LL_I2C_TransmitData8(MCU_PERIPH_I2C, MXC400_REG_OUT_START);
        } else {
#ifdef CONFIG_DEBUG_ACCEL
            cdc_debug("????\n");
#endif
        }
    } else {
#ifdef CONFIG_DEBUG_ACCEL
        cdc_debug("i2c: invalid state %x\n", cur_state);
#endif
    }
}

void TIM6_DAC_LPTIM1_IRQHandler(void) {
    LL_TIM_ClearFlag_UPDATE(MCU_ACCEL_TIM);

#ifdef CONFIG_DEBUG_ACCEL
    //cdc_debug("timer %d %x %x\n", state, MCU_PERIPH_I2C->ISR, timing);
#endif
    if (state == state_Idle) {
        state = state_SendAddr;
        LL_I2C_HandleTransfer(MCU_PERIPH_I2C,
                MXC400_I2C_ADDR,
                LL_I2C_ADDRSLAVE_7BIT,
                1,
                LL_I2C_MODE_SOFTEND,
                LL_I2C_GENERATE_START_WRITE);
    }
}

static void __write_control_reg(uint8_t control) {
    chip_detected = false;

    MCU_PERIPH_I2C->CR1 &= ~(I2C_CR1_TXIE | I2C_CR1_ERRIE | I2C_CR1_NACKIE);

    LL_I2C_HandleTransfer(MCU_PERIPH_I2C,
        MXC400_I2C_ADDR,
        LL_I2C_ADDRSLAVE_7BIT,
        2,
        LL_I2C_MODE_AUTOEND,
        LL_I2C_GENERATE_START_WRITE);

    LL_I2C_TransmitData8(MCU_PERIPH_I2C, MXC400_REG_CONTROL);
    while (!LL_I2C_IsActiveFlag_TXE(MCU_PERIPH_I2C)) {
        if (__i2c_err_detected()) {
            __i2c_err_clear();
            goto write_complete;
        }
    }
    LL_I2C_TransmitData8(MCU_PERIPH_I2C, control);
    while (LL_I2C_IsActiveFlag_BUSY(MCU_PERIPH_I2C)) {
        if (__i2c_err_detected())  {
            __i2c_err_clear();
            goto write_complete;
        }
    }

    MCU_PERIPH_I2C->CR1 |= (I2C_CR1_TXIE | I2C_CR1_ERRIE | I2C_CR1_NACKIE);

    chip_detected = true;

write_complete:
    mcu_update_dma_clock();
}

void accel_init(void) {
    LL_APB1_GRP1_EnableClock(LL_APB1_GRP1_PERIPH_I2C1);

    __i2c_disable();

    LL_I2C_SetTiming(MCU_PERIPH_I2C, timing);
    LL_I2C_EnableAnalogFilter(MCU_PERIPH_I2C);

    LL_I2C_Enable(MCU_PERIPH_I2C);

    LL_DMA_SetPeriphRequest(DMA1, MCU_DMA_CHANNEL_I2C, LL_DMAMUX_REQ_I2C1_RX);

    LL_DMA_SetDataTransferDirection(DMA1, MCU_DMA_CHANNEL_I2C, LL_DMA_DIRECTION_PERIPH_TO_MEMORY);
    LL_DMA_SetChannelPriorityLevel(DMA1, MCU_DMA_CHANNEL_I2C, LL_DMA_PRIORITY_LOW);
    LL_DMA_SetPeriphIncMode(DMA1, MCU_DMA_CHANNEL_I2C, LL_DMA_PERIPH_NOINCREMENT);
    LL_DMA_SetMemoryIncMode(DMA1, MCU_DMA_CHANNEL_I2C, LL_DMA_MEMORY_INCREMENT);
    LL_DMA_SetPeriphSize(DMA1, MCU_DMA_CHANNEL_I2C, LL_DMA_PDATAALIGN_BYTE);
    LL_DMA_SetMemorySize(DMA1, MCU_DMA_CHANNEL_I2C, LL_DMA_MDATAALIGN_BYTE);

    LL_DMA_EnableIT_TC(DMA1, MCU_DMA_CHANNEL_I2C);

    NVIC_SetPriority(DMA1_Ch4_7_DMA2_Ch1_5_DMAMUX_OVR_IRQn, MCU_IRQ_PRIORITY_I2C_DMA);
    NVIC_EnableIRQ(DMA1_Ch4_7_DMA2_Ch1_5_DMAMUX_OVR_IRQn);

    NVIC_SetPriority(I2C1_IRQn, MCU_IRQ_PRIORITY_I2C);
    NVIC_EnableIRQ(I2C1_IRQn);

    // let write control reg enable the remaining interrupts later
    LL_I2C_EnableIT_TC(MCU_PERIPH_I2C);

    LL_I2C_EnableDMAReq_RX(MCU_PERIPH_I2C);

    LL_APB1_GRP1_EnableClock(LL_APB1_GRP1_PERIPH_TIM6);

    LL_TIM_SetPrescaler(MCU_ACCEL_TIM, timer_prescaler);
    LL_TIM_SetAutoReload(MCU_ACCEL_TIM, TIMERHZ);
    LL_TIM_EnableUpdateEvent(MCU_ACCEL_TIM);
    LL_TIM_EnableIT_UPDATE(MCU_ACCEL_TIM);

    NVIC_SetPriority(TIM6_DAC_LPTIM1_IRQn, MCU_IRQ_PRIORITY_I2C_TIMER);
    NVIC_EnableIRQ(TIM6_DAC_LPTIM1_IRQn);

    // park the accelerometer until it is used
    __write_control_reg(MXC400_POWERDOWN);
}

void accel_deinit(void) {
    accel_enable_poll(false, 0);
    __i2c_disable();

    NVIC_DisableIRQ(TIM6_DAC_LPTIM1_IRQn);
    NVIC_DisableIRQ(I2C1_IRQn);
    NVIC_DisableIRQ(DMA1_Ch4_7_DMA2_Ch1_5_DMAMUX_OVR_IRQn);

    LL_APB1_GRP1_DisableClock(LL_APB1_GRP1_PERIPH_TIM6);
    LL_APB1_GRP1_DisableClock(LL_APB1_GRP1_PERIPH_I2C1);

    mcu_update_dma_clock();
}

bool accel_is_detected(void) {
    return chip_detected;
}

bool accel_is_enabled(void) {
    return chip_detected && LL_I2C_IsEnabled(MCU_PERIPH_I2C);
}

static void __poll_pause() {
    if (polling) {
#ifdef CONFIG_DEBUG_ACCEL
        //cdc_debug("poll pause... %x %x\n", MCU_PERIPH_I2C->CR1, MCU_PERIPH_I2C->CR2);
#endif
        LL_TIM_DisableCounter(MCU_ACCEL_TIM);
        while (state != state_Idle || LL_I2C_IsActiveFlag_BUSY(MCU_PERIPH_I2C));
#ifdef CONFIG_DEBUG_ACCEL
        //cdc_debug("done\n");
#endif
    }
}

static void __poll_resume() {
    if (polling && LL_I2C_IsEnabled(MCU_PERIPH_I2C) && chip_detected) {
#ifdef CONFIG_DEBUG_ACCEL
        //cdc_debug("resuming\n");
#endif
        LL_TIM_EnableCounter(MCU_ACCEL_TIM);
    }
}

void accel_adjust_i2c_timing(uint32_t freq) {
    // 100 kHz I2C frequency
    // using 100 ns rise and fall time
    // with analog filter enabled

    uint32_t new_timing;
    uint32_t new_prescaler = (freq / TIMERHZ) - 1;
    switch (freq) {
    case 4*1000*1000: new_timing = 0x00100D14; break;
    case 6*1000*1000: new_timing = 0x0020171D; break;
    case 12*1000*1000: new_timing = 0x00402D41; break;
    case 16*1000*1000: new_timing = 0x00503D58; break;
    case 24*1000*1000: new_timing = 0x00805C87; break;
    case 48*1000*1000: new_timing = 0x10805D88; break;
    default: new_timing = 0; break;
    }

    if (new_prescaler == timer_prescaler)
        return;

    timing = new_timing;
    timer_prescaler = new_prescaler;

    __poll_pause();

    if (timing != 0) {
        if (LL_I2C_IsEnabled(MCU_PERIPH_I2C)) {
            // already initialised

            __i2c_disable();
            LL_I2C_SetTiming(MCU_PERIPH_I2C, timing);
            LL_I2C_Enable(MCU_PERIPH_I2C);

            LL_TIM_SetPrescaler(MCU_ACCEL_TIM, timer_prescaler);

        }

        __poll_resume();
    }
}

bool accel_enable_poll(bool enable, uint32_t hz) {
    if (polling ^ enable) {
        __poll_pause();
        __write_control_reg(enable ? 0 : MXC400_POWERDOWN);

        polling = enable;
        LL_TIM_SetAutoReload(MCU_ACCEL_TIM, TIMERHZ / (enable ? hz : 1));
        __poll_resume();
    }

    return chip_detected;
}

void accel_copy_state(void* out) {
    // make sure the interrupt does not
    // fire midway through the copy
    NVIC_DisableIRQ(DMA1_Ch4_7_DMA2_Ch1_5_DMAMUX_OVR_IRQn);
    memcpy(out, &accel_data[visible_accel_state], sizeof(accel_data[0]));
    NVIC_EnableIRQ(DMA1_Ch4_7_DMA2_Ch1_5_DMAMUX_OVR_IRQn);
#ifdef CONFIG_DEBUG_ACCEL
    //cdc_debug("copy state %d\n", accel_data.axis[0]);
#endif
}
