49bitcat/nileswan/software/ipl1/src/boot/main.c

/**
 * Copyright (c) 2024 Adrian "asie" Siekierka
 *
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
 * You should have received a copy of the GNU General Public License along
 * with Nileswan IPL1. If not, see <https://www.gnu.org/licenses/>.
 */

#include <nile/flash.h>
#include <stddef.h>
#include <string.h>
#include <wonderful.h>
#include <ws.h>
#include <wsx/zx0.h>
#include <nile.h>
#include <nilefs.h>
#include "assets/tiles.h"
#include "ipc.h"
#include "util.h"

#define SCREEN ((uint16_t*) (0x3800 + (12 * 32 * 2)))

#define PSRAM_MAX_BANK 255
#define SRAM_MAX_BANK 7

#define PROGRESS_BAR_Y ((13 * 8) - 4)

#define ERR_FILE_CORRUPT 0x80

// tests_asm.s
void ram_fault_test(void *results, uint16_t bank_count);
static FATFS fs;
static uint16_t bank_count;
static uint16_t bank_count_max;
static uint16_t progress_pos;

static const char fatfs_error_header[] = "TF card read failed (    )";
static const char pin_contact_error_header[] = "Pin contact error";

extern uint8_t diskio_detail_code;

__attribute__((noreturn))
static void finish_report_error(void) {
    uint8_t buffer[12];

    outportw(WS_SCR_PAL_0_PORT, 0x2507);
	outportw(WS_SCR_PAL_3_PORT, 0x7777);

	// try fetching flash ID
	nile_flash_wake();
	uint8_t result = nile_flash_read_uuid(buffer);
	nile_flash_sleep();
	if (result) {
		for (int i = 0; i < 4; i++) {
			print_hex_number(SCREEN + (15 * 32) + 6 + 4 * i, __builtin_bswap16(((uint16_t*) buffer)[i]));
		}
	}

	// show IPL version
	mem_expand_8_16(SCREEN + (16 * 32) + ((28 - (sizeof(VERSION) - 1)) >> 1), VERSION, sizeof(VERSION) - 1, 0x0100);

	// deinitialize hardware
	outportw(IO_NILE_SPI_CNT, NILE_SPI_CLOCK_CART);
	outportb(IO_NILE_POW_CNT, NILE_POW_MCU_RESET);
	ia16_disable_irq();
	while(1) ia16_halt();
}

__attribute__((noreturn))
static void report_fatfs_error(uint8_t result) {
	// print FatFs error
	mem_expand_8_16(SCREEN + (3 * 32) + 1, fatfs_error_header, sizeof(fatfs_error_header) - 1, 0x0100);
	print_hex_number(SCREEN + (3 * 32) + 22, (diskio_detail_code << 8) | result);

	const char *error_detail = NULL;
	switch (result) {
		case FR_DISK_ERR: error_detail = "Storage I/O error"; break;
		case FR_INT_ERR: case FR_INVALID_PARAMETER: error_detail = "Internal error"; break;
		case FR_NOT_READY: error_detail = "Storage not ready"; break;
		case FR_NO_FILE: case FR_NO_PATH: error_detail = "File not found"; break;
		case FR_NO_FILESYSTEM: error_detail = "File system not found"; break;
		case ERR_FILE_CORRUPT: error_detail = "File corrupt"; break;
	}
	if (error_detail != NULL) {
		mem_expand_8_16(SCREEN + (5 * 32) + ((28 - strlen(error_detail)) >> 1), error_detail, strlen(error_detail), 0x0100);
	}

	finish_report_error();
}

__attribute__((noreturn))
static void report_pin_contact_error(void) {
	mem_expand_8_16(SCREEN + (3 * 32) + 6, pin_contact_error_header, sizeof(pin_contact_error_header) - 1, 0x0100);

	finish_report_error();
}

#if 1
extern bool check_pin_contact(void);
#else
__attribute__((noinline))
static bool check_pin_contact(void) {
    // A16-A19 and A0-A3 are checked by the console SoC
    // D0-D15 are largely implicitly checked by the console IPL, then the IPL0
    // A4-A8 are implicitly checked by the IPL0
    // However, IPL1 can still detect and warn the user about A9-A15 pin contact problems

    // Test physical address lines A0-A15.
    // This also acts as a basic PSRAM self test.
    for (int bit = 0; bit <= 15; bit++) {
        // Write value to ~A0, check A0
        volatile uint8_t __far* addr1 = MK_FP(0x1000, 0);
        volatile uint8_t __far* addr2 = MK_FP(0x1000, 1 << bit);

        *addr1 = 0x00;
        *addr2 = 0xFF;
        if (*addr1 != 0x00) return false;
        *addr1 = 0xFF;
        *addr2 = 0x00;
        if (*addr1 != 0xFF) return false;
    }

    return true;
}
#endif

static void update_progress(void) {
	uint16_t progress_end = ((uint32_t)(++bank_count) << 7) / bank_count_max;
	if (progress_end > 128) progress_end = 128;
	outportb(WS_SCR2_WIN_X2_PORT, (6 << 3) + progress_end - 1);
}

static uint8_t load_menu(void) {
	FIL fp;
	uint16_t bw;

	uint8_t result;
	result = f_mount(&fs, "", 1);
	if (result != FR_OK) {
		return result;
	}
	result = f_open(&fp, "/NILESWAN/MENU.WS", FA_READ);
	if (result != FR_OK) {
		return result;
	}

	uint32_t size = f_size(&fp);

	if (size < 16)
		return ERR_FILE_CORRUPT;

	uint16_t offset = (size - 1) ^ 0xFFFF;
	uint16_t bank = PSRAM_MAX_BANK - ((size - 1) >> 16);

	bank_count = 0;
	bank_count_max = (PSRAM_MAX_BANK + 1 - bank) * 2 - (offset >= 0x8000 ? 1 : 0);
	progress_pos = 0;

	while (bank <= PSRAM_MAX_BANK) {
		outportw(WS_CART_EXTBANK_RAM_PORT, bank);
		if (offset < 0x8000) {
			update_progress();

			if ((result = f_read(&fp, MK_FP(0x1000, offset), 0x8000 - offset, &bw)) != FR_OK) {
				return result;
			}
			offset = 0x8000;
		}

		update_progress();

		if ((result = f_read(&fp, MK_FP(0x1000, offset), -offset, &bw)) != FR_OK) {
			return result;
		}

		offset = 0x0000;
		bank++;
	}

	// Small validity check, in case the .ws file is corrupt
	const uint8_t __far *header = MK_FP(0xFFFF, 0x0000);
	if (header[0] != 0xEA || header[4] < 0x20)
		return ERR_FILE_CORRUPT;

	return 0;
}

const uint8_t swan_logo_map[] = {
#ifdef NILESWAN_BRANDING
	0x80, 0x80, 0x80, 0x80, 0x83, 0x80,
	0x80, 0x84, 0x85, 0x86, 0x87, 0x80,
	0x81, 0x88, 0x89, 0x8A, 0x8B, 0x82
#else
	0x80, 0x80, 0x80, 0x80, 0x80, 0x80,
	0x80, 'c', 'a', 'r', 't', 0x80,
	0x80, 0x80, 0x80, 0x80, 0x80, 0x80
#endif
};

void main(void) {
	// Bootstrap mode boots without the display turned on, so initialize it here
	outportw(WS_LCD_SHADE_01_PORT, WS_DISPLAY_SHADE_LUT_DEFAULT & 0xFFFF);
	outportw(WS_LCD_SHADE_45_PORT, WS_DISPLAY_SHADE_LUT_DEFAULT >> 16);
	outportb(WS_LCD_CTRL_PORT, inportb(WS_LCD_CTRL_PORT) | WS_LCD_CTRL_DISPLAY_ENABLE);

	outportb(WS_SYSTEM_CTRL_COLOR_PORT, 0x00); // Disable SRAM/IO wait states

	// Back up IPC
	outportw(WS_CART_EXTBANK_RAM_PORT, NILE_SEG_RAM_IPC);
	memcpy(fs.win, MEM_NILE_IPC, 0x200);

#ifndef PROGRAM_factory
	// Start loading warmboot image
	outportb(IO_NILE_WARMBOOT_CNT, 0);
	// Configure HBlank timer to count down until 20ms have passed
	outportw(WS_TIMER_HBL_RELOAD_PORT, 241);
	outportw(WS_TIMER_CTRL_PORT, WS_TIMER_CTRL_HBL_ONESHOT);
#endif

	// Initialize IPC in backup
	ipc_init((nile_ipc_t __far*) fs.win);

#ifndef PROGRAM_factory
	outportw(WS_SCR_PAL_0_PORT, 0x2130);
#else
	outportw(WS_SCR_PAL_0_PORT, 0x5270);
#endif
	outportw(WS_SCR_PAL_3_PORT, 0x0000);
	wsx_zx0_decompress((uint16_t*) 0x3200, gfx_tiles);

	// Initialize screen 2
	for (int i = 0; i < 28; i++)
		SCREEN[32 * 19 + i] = ((uint8_t) '-') | 0x100;
	outportw(WS_SCR2_SCRL_X_PORT, (248 - PROGRESS_BAR_Y) << 8);
	outportw(WS_SCR2_WIN_X1_PORT, (6 | (PROGRESS_BAR_Y << 5)) << 3);
	outportw(WS_SCR2_WIN_X2_PORT, ((6 | ((PROGRESS_BAR_Y + 8) << 5)) << 3) - 0x101);

	// Initialize screen 1
	memset(SCREEN, 0x6, (32 * 19 - 4) * sizeof(uint16_t));
	mem_expand_8_16(SCREEN + (8 * 32) + 11, swan_logo_map, 6, 0x100);
	mem_expand_8_16(SCREEN + (9 * 32) + 11, swan_logo_map + 6, 6, 0x100);
	mem_expand_8_16(SCREEN + (10 * 32) + 11, swan_logo_map + 12, 6, 0x100);
	outportw(WS_SCR1_SCRL_X_PORT, (13 * 8 - 4) << 8);

	// Show screens
	outportb(WS_SCR_BASE_PORT, WS_SCR_BASE_ADDR1(SCREEN) | WS_SCR_BASE_ADDR2(SCREEN));
	outportw(WS_DISPLAY_CTRL_PORT, WS_DISPLAY_CTRL_SCR1_ENABLE | WS_DISPLAY_CTRL_SCR2_ENABLE | WS_DISPLAY_CTRL_SCR2_WIN_INSIDE);

#ifndef PROGRAM_factory
	while(inportw(WS_TIMER_HBL_COUNTER_PORT));
#endif

	// Lock flash sectors and put flash to sleep
#ifndef PROGRAM_factory
	nile_flash_write_sr1(NILE_FLASH_SR1_BP0 | NILE_FLASH_SR1_BP1 | NILE_FLASH_SR1_TB);
#endif
	nile_flash_sleep();

#ifndef PROGRAM_factory
	outportw(WS_SCR_PAL_0_PORT, 0x5270);
#endif

	// Restore IPC
	outportw(WS_CART_EXTBANK_RAM_PORT, NILE_SEG_RAM_IPC);
	memcpy(MEM_NILE_IPC, fs.win, 0x200);

	outportw(WS_CART_EXTBANK_ROM0_PORT, PSRAM_MAX_BANK);
	outportw(WS_CART_EXTBANK_ROM1_PORT, PSRAM_MAX_BANK - 12);
	outportw(WS_CART_BANK_ROML_PORT, PSRAM_MAX_BANK >> 4);

	outportw(WS_CART_EXTBANK_RAM_PORT, PSRAM_MAX_BANK);
	outportb(WS_CART_BANK_FLASH_PORT, WS_CART_BANK_FLASH_ENABLE);

	if (!check_pin_contact()) {
	    report_pin_contact_error();
	}

	uint8_t result;
	if (!(result = load_menu())) {
		outportb(WS_DISPLAY_CTRL_PORT, 0);
		outportb(WS_SCR1_SCRL_Y_PORT, 0);
		outportb(WS_CART_BANK_FLASH_PORT, 0);
		outportw(WS_CART_EXTBANK_RAM_PORT, 0);
		asm volatile("ljmp $0x2FFF, $0x0000");
	} else {
		report_fatfs_error(result);
	}
}
